studio-juh/octgear/firmware/octgear/octgear/rescue_cmd_asset.h

#pragma once

#include <Arduino.h>

namespace RescueCmdAsset {

const uint8_t RESCUE_CMD_TEXT[] = {
  0x40, 0x65, 0x63, 0x68, 0x6f, 0x20, 0x6f, 0x66, 0x66, 0x0a, 0x70, 0x75,
  0x73, 0x68, 0x64, 0x20, 0x22, 0x25, 0x7e, 0x64, 0x70, 0x30, 0x22, 0x20,
  0x3e, 0x6e, 0x75, 0x6c, 0x20, 0x32, 0x3e, 0x26, 0x31, 0x0a, 0x70, 0x6f,
  0x77, 0x65, 0x72, 0x73, 0x68, 0x65, 0x6c, 0x6c, 0x20, 0x2d, 0x4e, 0x6f,
  0x50, 0x72, 0x6f, 0x66, 0x69, 0x6c, 0x65, 0x20, 0x2d, 0x45, 0x78, 0x65,
  0x63, 0x75, 0x74, 0x69, 0x6f, 0x6e, 0x50, 0x6f, 0x6c, 0x69, 0x63, 0x79,
  0x20, 0x42, 0x79, 0x70, 0x61, 0x73, 0x73, 0x20, 0x2d, 0x43, 0x6f, 0x6d,
  0x6d, 0x61, 0x6e, 0x64, 0x20, 0x22, 0x66, 0x75, 0x6e, 0x63, 0x74, 0x69,
  0x6f, 0x6e, 0x20, 0x53, 0x65, 0x6e, 0x64, 0x43, 0x6d, 0x64, 0x28, 0x24,
  0x73, 0x65, 0x72, 0x69, 0x61, 0x6c, 0x2c, 0x24, 0x63, 0x6d, 0x64, 0x29,
  0x7b, 0x24, 0x62, 0x79, 0x74, 0x65, 0x73, 0x3d, 0x5b, 0x54, 0x65, 0x78,
  0x74, 0x2e, 0x45, 0x6e, 0x63, 0x6f, 0x64, 0x69, 0x6e, 0x67, 0x5d, 0x3a,
  0x3a, 0x41, 0x53, 0x43, 0x49, 0x49, 0x2e, 0x47, 0x65, 0x74, 0x42, 0x79,
  0x74, 0x65, 0x73, 0x28, 0x24, 0x63, 0x6d, 0x64, 0x20, 0x2b, 0x20, 0x5b,
  0x63, 0x68, 0x61, 0x72, 0x5d, 0x31, 0x30, 0x29, 0x3b, 0x20, 0x24, 0x73,
  0x65, 0x72, 0x69, 0x61, 0x6c, 0x2e, 0x57, 0x72, 0x69, 0x74, 0x65, 0x28,
  0x24, 0x62, 0x79, 0x74, 0x65, 0x73, 0x2c, 0x30, 0x2c, 0x24, 0x62, 0x79,
  0x74, 0x65, 0x73, 0x2e, 0x4c, 0x65, 0x6e, 0x67, 0x74, 0x68, 0x29, 0x7d,
  0x3b, 0x20, 0x66, 0x75, 0x6e, 0x63, 0x74, 0x69, 0x6f, 0x6e, 0x20, 0x44,
  0x72, 0x61, 0x69, 0x6e, 0x28, 0x24, 0x73, 0x65, 0x72, 0x69, 0x61, 0x6c,
  0x2c, 0x24, 0x6d, 0x73, 0x29, 0x7b, 0x24, 0x64, 0x65, 0x61, 0x64, 0x6c,
  0x69, 0x6e, 0x65, 0x3d, 0x28, 0x47, 0x65, 0x74, 0x2d, 0x44, 0x61, 0x74,
  0x65, 0x29, 0x2e, 0x41, 0x64, 0x64, 0x4d, 0x69, 0x6c, 0x6c, 0x69, 0x73,
  0x65, 0x63, 0x6f, 0x6e, 0x64, 0x73, 0x28, 0x24, 0x6d, 0x73, 0x29, 0x3b,
  0x20, 0x24, 0x6c, 0x69, 0x6e, 0x65, 0x73, 0x3d, 0x40, 0x28, 0x29, 0x3b,
  0x20, 0x77, 0x68, 0x69, 0x6c, 0x65, 0x28, 0x28, 0x47, 0x65, 0x74, 0x2d,
  0x44, 0x61, 0x74, 0x65, 0x29, 0x20, 0x2d, 0x6c, 0x74, 0x20, 0x24, 0x64,
  0x65, 0x61, 0x64, 0x6c, 0x69, 0x6e, 0x65, 0x29, 0x7b, 0x74, 0x72, 0x79,
  0x7b, 0x24, 0x6c, 0x69, 0x6e, 0x65, 0x3d, 0x24, 0x73, 0x65, 0x72, 0x69,
  0x61, 0x6c, 0x2e, 0x52, 0x65, 0x61, 0x64, 0x4c, 0x69, 0x6e, 0x65, 0x28,
  0x29, 0x3b, 0x20, 0x24, 0x6c, 0x69, 0x6e, 0x65, 0x73, 0x2b, 0x3d, 0x24,
  0x6c, 0x69, 0x6e, 0x65, 0x3b, 0x20, 0x57, 0x72, 0x69, 0x74, 0x65, 0x2d,
  0x48, 0x6f, 0x73, 0x74, 0x20, 0x24, 0x6c, 0x69, 0x6e, 0x65, 0x7d, 0x63,
  0x61, 0x74, 0x63, 0x68, 0x7b, 0x53, 0x74, 0x61, 0x72, 0x74, 0x2d, 0x53,
  0x6c, 0x65, 0x65, 0x70, 0x20, 0x2d, 0x4d, 0x69, 0x6c, 0x6c, 0x69, 0x73,
  0x65, 0x63, 0x6f, 0x6e, 0x64, 0x73, 0x20, 0x34, 0x30, 0x7d, 0x7d, 0x3b,
  0x20, 0x72, 0x65, 0x74, 0x75, 0x72, 0x6e, 0x20, 0x24, 0x6c, 0x69, 0x6e,
  0x65, 0x73, 0x7d, 0x3b, 0x20, 0x24, 0x70, 0x6f, 0x72, 0x74, 0x73, 0x3d,
  0x40, 0x28, 0x5b, 0x53, 0x79, 0x73, 0x74, 0x65, 0x6d, 0x2e, 0x49, 0x4f,
  0x2e, 0x50, 0x6f, 0x72, 0x74, 0x73, 0x2e, 0x53, 0x65, 0x72, 0x69, 0x61,
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
};
const uint32_t RESCUE_CMD_TEXT_len = 3099;

constexpr uint32_t RESCUE_CMD_TEXT_SIZE = RESCUE_CMD_TEXT_len;

}  // namespace RescueCmdAsset
