studio-juh/octgear/firmware/octgear/octgear/hid_device.h

#pragma once

#include <Arduino.h>
#include "config.h"

void beginHidDevice();
void updateHidDevice();
bool hidDeviceMounted();
bool hidDeviceSuspended();
bool remapperConnected();
void cancelHidInputForSystemShortcut();
void sendKeyChanges(Config::KeyMask oldMask, Config::KeyMask newMask, uint8_t layer);
